lucasjmina/arduino-datalogger/board/arduino_datalogger.kicad_sch

## KiCad design board/arduino_datalogger.kicad_sch (2023-12-18)

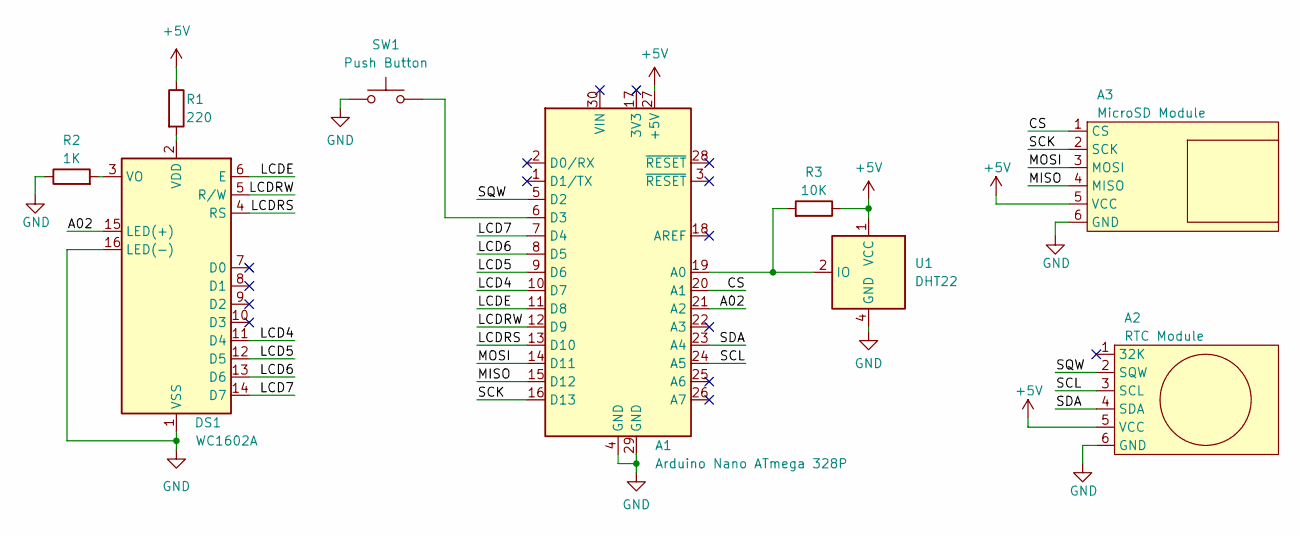
[picture p6: schematic arduino_datalogger.kicad_sch]

Parts:
A1: Arduino Nano ATmega 328P; Arduino_Nano
A2: RTC Module
A3: MicroSD Module
DS1: WC1602A
R1: 220; R_Axial_DIN0207_L6.3mm_D2.5mm_P7.62mm_Horizontal
R2: 1K; R_Axial_DIN0207_L6.3mm_D2.5mm_P7.62mm_Horizontal
R3: 10K; R_Axial_DIN0207_L6.3mm_D2.5mm_P7.62mm_Horizontal
SW1: Push Button; SW_PUSH-12mm
U1: DHT22; Aosong_DHT11_5.5x12.0_P2.54mm

Connections:
+5V: A1.27 (+5V), A2.5 (VCC), A3.5 (VCC), R1.1, R3.1, U1.1 (VCC)
A02: A1.21 (A2), DS1.15 (LED(+))
CS: A1.20 (A1), A3.1 (CS)
GND: A1.4 (GND), A1.29 (GND), A2.6 (GND), A3.6 (GND), DS1.1 (VSS), DS1.16 (LED(-)), R2.1, SW1.1, U1.4 (GND)
LCD4: A1.10 (D7), DS1.11 (D4)
LCD5: A1.9 (D6), DS1.12 (D5)
LCD6: A1.8 (D5), DS1.13 (D6)
LCD7: A1.7 (D4), DS1.14 (D7)
LCDE: A1.11 (D8), DS1.6 (E)
LCDRS: A1.13 (D10), DS1.4 (RS)
LCDRW: A1.12 (D9), DS1.5 (R/W)
MISO: A1.15 (D12), A3.4 (MISO)
MOSI: A1.14 (D11), A3.3 (MOSI)
unnamed: A1.6 (D3), SW1.2
unnamed: A1.19 (A0), R3.2, U1.2 (IO)
unnamed: DS1.2 (VDD), R1.2
unnamed: DS1.3 (VO), R2.2
SCK: A1.16 (D13), A3.2 (SCK)
SCL: A1.24 (A5), A2.3 (SCL)
SDA: A1.23 (A4), A2.4 (SDA)
SQW: A1.5 (D2), A2.2 (SQW)
